lightrail-dev/new/docs/chip_design/NCE_Block_Diagram.md

# NCE (Neural Compute Engine) — Internal Block Diagram

**Document:** LR-NCE-BLK-001  
**Revision:** 1.0  
**Date:** 2026-05-26  
**Process Node:** SMIC 28nm HPC+ / 40nm LL  
**Company:** LightRail AI  

---

## 1. Top-Level Block Diagram

```
+===========================================================================================+
|                              NCE SoC Die (BGA-2500)                                       |
|                                                                                           |
|  +-------+  +-------+  +-------+  +-------+                                              |
|  | JTAG  |  | PMBus |  | SPI   |  | I2C   |     <-- Management I/O (NW corner)           |
|  | Debug |  | Mgmt  |  | Flash |  | Bus   |                                              |
|  +---+---+  +---+---+  +---+---+  +---+---+                                              |
|      |          |          |          |                                                    |
|      +----------+----------+----------+                                                   |
|                 |                                                                         |
|           +-----+------+                                                                  |
|           | System Bus |    AXI4 Interconnect Fabric (250 MHz)                            |
|           | Crossbar   +----------------------------------------------------------+       |
|           +--+---------+--+-----------+--+-----------+--+-----------+--+          |       |
|              |            |             |              |              |            |       |
|              v            v             v              v              v            v       |
|  +-----------+--+ +------+------+ +----+------+ +-----+-----+ +-----+-----+ +----+----+  |
|  | COMPUTE      | | MEMORY      | | PHOTONIC  | | QPA       | | HOST      | | POWER   |  |
|  | CLUSTER      | | SUBSYSTEM   | | I/O       | | CONTROL   | | INTERFACE | | MGMT    |  |
|  +-----------+--+ +------+------+ +----+------+ +-----+-----+ +-----+-----+ +----+----+  |
|              |            |             |              |              |            |       |
|  (detail     |  (detail   |  (detail    |   (detail    |   (detail    |  (detail   |      |
|   below)     |   below)   |   below)    |    below)    |    below)    |   below)   |      |
|              |            |             |              |              |            |       |
+===========================================================================================+
```

---

## 2. Compute Cluster Block Diagram

```
+=========================================================================+
|                        COMPUTE CLUSTER                                  |
|                                                                         |
|  +------------------------------------------------------------------+  |
|  |                    Instruction Frontend                           |  |
|  |  +----------------+  +-----------------+  +-------------------+  |  |
|  |  | Instr Fetch    |  | Instr Decode    |  | Issue / Dispatch  |  |  |
|  |  | Unit (IFU)     |->| Unit (IDU)      |->| Unit              |  |  |
|  |  | L1 I$ 64KB     |  | bfloat16/24     |  | In-order SIMD     |  |  |
|  |  | 4-way assoc    |  | INT8, FP32      |  | Scalar bypass     |  |  |
|  |  +----------------+  +-----------------+  +--------+----------+  |  |
|  +------------------------------------------------------------------+  |
|                                                       |                |
|                                    +------------------+--------+       |
|                                    |                           |       |
|                                    v                           v       |
|  +----------------------------------+   +------------------------+     |
|  |     SIMD Execution Engine        |   | Scalar Execution Unit  |     |
|  |                                  |   |                        |     |
|  |  +----------------------------+  |   | +--------------------+ |     |
|  |  | 128-way SIMD Array         |  |   | | ALU (INT/FP)       | |     |
|  |  | 8 clusters x 16 lanes     |  |   | | Branch Unit        | |     |
|  |  |                            |  |   | | Address Gen        | |     |
|  |  | Each lane:                 |  |   | +--------------------+ |     |
|  |  |   bfloat16 MAC unit        |  |   +------------------------+     |
|  |  |   bfloat24 MAC unit        |  |                                  |
|  |  |   INT8 MAC unit (4x pack)  |  |                                  |
|  |  |   FP32 accumulator         |  |                                  |
|  |  +----------------------------+  |                                  |
|  |                                  |                                  |
|  |  +----------------------------+  |                                  |
|  |  | Register File              |  |                                  |
|  |  | 16x Matrix Regs (256-bit)  |  |                                  |
|  |  | 16x Vector Regs (256-bit)  |  |                                  |
|  |  | 8x Scalar Regs (64-bit)    |  |                                  |
|  |  +----------------------------+  |                                  |
|  +----------------------------------+                                  |
|                     |                                                  |
|                     v                                                  |
|  +----------------------------------+                                  |
|  |      Memory Access Pipeline      |                                  |
|  |  +-------------+  +----------+   |                                  |
|  |  | Load/Store  |  | L1 D$    |   |                                  |
|  |  | Unit (LSU)  |->| 128 KB   |   |                                  |
|  |  | Scatter/    |  | 8-way    |   |                                  |
|  |  | Gather      |  | assoc    |   |                                  |
|  |  +-------------+  +----+-----+   |                                  |
|  +----------------------------------+                                  |
|                            |                                           |
|                            v                                           |
|  +----------------------------------+                                  |
|  |       L2 Cache (Shared)          |                                  |
|  |  16 MB, 8-way, inclusive         |                                  |
|  |  64-byte lines, write-back       |                                  |
|  |  4 DMA channels (scatter-gather) |                                  |
|  +----------------------------------+                                  |
|                                                                        |
+========================================================================+
```

**Function:** Executes AI/ML tensor operations (matrix multiply, convolution,
activation) on streaming data. The 128-way SIMD array processes 128 bfloat16
multiply-accumulate operations per cycle. Data flows from HBM5 through the
cache hierarchy into the register file, and results can be sent to the TFLN
photonic I/O for distributed all-reduce.

---

## 3. Memory Subsystem Block Diagram (HBM5)

```
+=========================================================================+
|                      MEMORY SUBSYSTEM (HBM5)                            |
|                                                                         |
|  +------------------------------------------------------------------+  |
|  |                 L3 / Last-Level Cache                             |  |
|  |  64 MB, 16-way set-associative, exclusive of L2                  |  |
|  |  128-byte lines, write-back, pseudo-LRU                          |  |
|  |  Coherence: MOESI (for CXL.mem shared memory)                    |  |
|  +---+------------------------------------------+-------------------+  |
|      |                                          |                      |
|      v                                          v                      |
|  +---+------------------------+  +--------------+-------------------+  |
|  | HBM5 Memory Scheduler      |  | HBM5 Side-Channel Controller    |  |
|  | & Request Queue             |  |                                  |  |
|  | - 4-entry queue per PC      |  | - REFCK_P/N generation           |  |
|  | - Age-based priority        |  | - CATTRIP / PWR_GOOD monitoring  |  |
|  | - Bank interleaving (32 bk) |  | - IEEE 1500 JTAG                 |  |
|  | - Per-bank refresh w/ temp  |  | - Temperature readout            |  |
|  |   compensation (1x/2x/4x)  |  | - Stack power management         |  |
|  | - R/W turnaround (tWTR/tRTW)|  |                                  |  |
|  +---+------------------------+  +---+------------------------------+  |
|      |                               |                                 |
|      v                               |                                 |
|  +---+-----------------------------+ |                                 |
|  | HBM5 Inline ECC Engine          | |                                 |
|  | - SECDED per 64-bit granule     | |                                 |
|  | - CE/UE counters & interrupt    | |                                 |
|  | - Background scrub (optional)   | |                                 |
|  +---+-----------------------------+ |                                 |
|      |                               |                                 |
|      v                               v                                 |
|  +---+-------------------------------------------------+               |
|  |           HBM5 PHY Controller                       |               |
|  |                                                     |               |
|  |  Stack 0         Stack 1         Stack 2         Stack 3            |
|  |  +------------+  +------------+  +------------+  +------------+    |
|  |  |16-Hi, 16PC |  |16-Hi, 16PC |  |16-Hi, 16PC |  |16-Hi, 16PC |    |
|  |  |1024b/PC    |  |1024b/PC    |  |1024b/PC    |  |1024b/PC    |    |
|  |  |8 Gbps/pin  |  |8 Gbps/pin  |  |8 Gbps/pin  |  |8 Gbps/pin  |    |
|  |  |1.28 TB/s   |  |1.28 TB/s   |  |1.28 TB/s   |  |1.28 TB/s   |    |
|  |  |64 GB       |  |64 GB       |  |64 GB       |  |64 GB       |    |
|  |  +------------+  +------------+  +------------+  +------------+    |
|  |                                                     |               |
|  |  Total: 64 PCs, 5.12 TB/s aggregate, 256 GB         |               |
|  |  (All lanes routed on silicon interposer)            |               |
|  +-----------------------------------------------------+               |
|                                                                         |
|  Data Storage Path:                                                     |
|    CXL -> AXI -> Scheduler -> ACT -> tRCD -> WR -> DQ+ECC -> DRAM      |
|                                                                         |
|  Data Retrieval Path:                                                   |
|    DRAM -> DQ -> ECC Check -> Scheduler -> L1/L2/RegFile/CXL Read       |
|                                                                         |
+=========================================================================+
```

**Function:** Provides 5.12 TB/s memory bandwidth to the compute cluster via
four HBM5 16-Hi stacks (64 pseudo-channels total, 256 GB capacity). The L3
cache serves as a victim cache for L2 misses. The memory scheduler implements
per-PC request queuing with age-based priority, bank-level parallelism,
read/write turnaround optimization, inline SECDED ECC, and temperature-
compensated per-bank refresh for data integrity and retention.

---

## 4. Photonic I/O Subsystem Block Diagram

```
+=========================================================================+
|                    PHOTONIC I/O SUBSYSTEM                               |
|                                                                         |
|  +------------------------------------------------------------------+  |
|  |                     TX Path (8 channels)                          |  |
|  |                                                                   |  |
|  |  +----------+  +----------+  +----------+  +----------+          |  |
|  |  | TX DSP   |  | PAM4     |  | DAC      |  | RF Drive |  --> To  |  |
|  |  | 3-tap    |->| Encoder  |->| (SerDes  |->| Buffer   |  TFLN   |  |
|  |  | FFE      |  |          |  |  analog) |  | +/- 1.5V |  PIC    |  |
|  |  +----------+  +----------+  +----------+  +----------+          |  |
|  |                                                                   |  |
|  +------------------------------------------------------------------+  |
|                                                                         |
|  +------------------------------------------------------------------+  |
|  |                     RX Path (8 channels)                          |  |
|  |                                                                   |  |
|  |  From   +----------+  +----------+  +----------+  +----------+   |  |
|  |  TFLN ->| TIA /    |->| ADC      |->| PAM4     |->| RX DSP   |   |  |
|  |  PIC    | AGC      |  | (SerDes  |  | Decoder  |  | CTLE +   |   |  |
|  |         |          |  |  analog) |  |          |  | 7-tap DFE|   |  |
|  |         +----------+  +----------+  +----------+  +----------+   |  |
|  |                                                                   |  |
|  +------------------------------------------------------------------+  |
|                                                                         |
|  +------------------------------------------------------------------+  |
|  |                   CDR & Link Training                             |  |
|  |                                                                   |  |
|  |  +-------------------+  +-------------------+                     |  |
|  |  | Clock Data        |  | Link Training     |                     |  |
|  |  | Recovery (CDR)    |  | State Machine     |                     |  |
|  |  | per-lane          |  | Auto-negotiation  |                     |  |
|  |  | 0.1 UI tolerance  |  | Loopback modes    |                     |  |
|  |  +-------------------+  +-------------------+                     |  |
|  |                                                                   |  |
|  +------------------------------------------------------------------+  |
|                                                                         |
|  Channel Summary:                                                       |
|  8 TX + 8 RX = 16 lanes total                                          |
|  200 Gbps PAM4 per lane = 1.6 Tbps half-duplex                         |
|  Direct-drive to TFLN modulator (zero-copper datapath)                  |
|  1550 nm C-band DWDM, 100 GHz channel spacing                          |
|                                                                         |
+=========================================================================+
```

**Function:** Converts electrical data from the compute cluster into optical
signals via direct-drive TFLN modulators. The TX path applies DSP equalization,
encodes to PAM4, and drives the TFLN MZI electrodes. The RX path receives
optical signals from photodetectors, digitizes, and recovers data with adaptive
equalization.

---

## 5. QPA Control Subsystem Block Diagram

```
+=========================================================================+
|                    QPA CONTROL SUBSYSTEM                                |
|                                                                         |
|  CXL 2.0 Memory-Mapped Interface                                       |
|  Base: 0x0000_1000                                                      |
|                                                                         |
|  +------------------------------------------------------------------+  |
|  |              CXL Register Decoder                                 |  |
|  |                                                                   |  |
|  |  0x1000: PHASE_SET      -- Write phase vector into shadow buffer  |  |
|  |  0x1004: TRIGGER_EXEC   -- Atomic commit shadow -> DAC bus        |  |
|  |  0x1008: STATUS         -- Read trigger state & channel health    |  |
|  |  0x100C: FAULT_MASK     -- Per-channel fault enable mask          |  |
|  |  0x1010: TELEMETRY_CTRL -- Telemetry sampling on/off              |  |
|  +---+------+----------+--------+------+----------------------------+  |
|      |      |          |        |      |                               |
|      v      v          |        v      v                               |
|  +---+---+ +--+--+     |  +----+---+ ++----+                          |
|  |Shadow | |Trig | |   |  |Fault   | |Telem|                          |
|  |Buffer | |Pipe | |   |  |Mask    | |Ctrl |                          |
|  |128-bit| |line | |   |  |Reg     | |Reg  |                          |
|  +---+---+ +--+--+     |  +----+---+ +--+--+                          |
|      |        |         |       |        |                             |
|      v        v         |       v        v                             |
|  +---+--------+---+    |  +----+--------+---+                         |
|  | DAC Phase Bus  |    |  | Telemetry Status |                        |
|  | 8ch x 16-bit   |    |  | {fault_cnt[15:0],|                        |
|  | Zero-skew sync |    |  |  trig_cnt[15:0]} |                        |
|  +-------+---------+    |  +-----------------+                         |
|          |              |                                              |
|          v              v                                              |
|  +-------+---------+  +---+-------------------+                       |
|  | 100 GHz DACs    |  | SNSPD Fault Detector  |                       |
|  | (external)      |  | 3 dB drop detection   |                       |
|  | Interleaved     |  | Per-channel latch      |                       |
|  +-----------------+  | Auto-reroute output    |                       |
|                       +------------------------+                       |
|                                                                        |
+=========================================================================+
```

**Function:** Provides real-time programmable control of the MZI photonic mesh.
The shadow buffer allows atomic updates of all phase channels simultaneously.
A one-cycle pipeline ensures zero-skew synchronization between phase setting
and DAC trigger. SNSPD feedback detects optical power drops and triggers
automatic waveguide rerouting.

---

## 6. Host Interface Block Diagram

```
+=========================================================================+
|                      HOST INTERFACE                                     |
|                                                                         |
|  +------------------------------------------------------------------+  |
|  |              PCIe Gen 6.0 Root Complex                            |  |
|  |                                                                   |  |
|  |  Port 0 (x16)                    Port 1 (x16)                    |  |
|  |  +-------------------+           +-------------------+           |  |
|  |  | 16 lanes          |           | 16 lanes          |           |  |
|  |  | 64 GT/s PAM4      |           | 64 GT/s PAM4      |           |  |
|  |  | 128 GB/s bidir    |           | 128 GB/s bidir    |           |  |
|  |  +-------------------+           +-------------------+           |  |
|  |                                                                   |  |
|  +------------------------------------------------------------------+  |
|                                                                         |
|  +------------------------------------------------------------------+  |
|  |              CXL 2.0 Controller (Type 2)                          |  |
|  |                                                                   |  |
|  |  +-------------+  +-------------+  +-------------+               |  |
|  |  | CXL.io      |  | CXL.cache   |  | CXL.mem     |               |  |
|  |  | (PCIe TLP)  |  | (coherent   |  | (shared     |               |  |
|  |  |             |  |  cache)     |  |  memory)    |               |  |
|  |  +-------------+  +-------------+  +-------------+               |  |
|  |                                                                   |  |
|  +------------------------------------------------------------------+  |
|                                                                         |
|  +------------------------------------------------------------------+  |
|  |              Debug & Management                                   |  |
|  |                                                                   |  |
|  |  +----------+  +----------+  +----------+  +----------+          |  |
|  |  | JTAG     |  | PMBus    |  | I2C      |  | SPI      |          |  |
|  |  | IEEE1149 |  | 1.3.1    |  | 400 kHz  |  | Flash    |          |  |
|  |  | IEEE1500 |  | VRM tele |  | HBM4 SPD |  | FW boot  |          |  |
|  |  +----------+  +----------+  +----------+  +----------+          |  |
|  |                                                                   |  |
|  +------------------------------------------------------------------+  |
|                                                                         |
+=========================================================================+
```

---
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
