lightrail-dev/new/fab/Dual_NCE_Accelerator_Fab_Release_v1/assembly/Dual_NCE_Accelerator_BOM.csv

Item | Designator | Quantity | Value | Footprint | Manufacturer | MPN | Distributor | DistributorPN | Package | Description | DNP
1 | ? | 1 | MountingHole:MountingHole_3.2mm_M3 | M3 Mounting Hole |  |  |  |  | M3 Mounting Hole |  | No
2 | ? | 1 | MountingHole:MountingHole_3.2mm_M3 | M3 Mounting Hole |  |  |  |  | M3 Mounting Hole |  | No
3 | ? | 1 | MountingHole:MountingHole_3.2mm_M3 | M3 Mounting Hole |  |  |  |  | M3 Mounting Hole |  | No
4 | ? | 1 | MountingHole:MountingHole_3.2mm_M3 | M3 Mounting Hole |  |  |  |  | M3 Mounting Hole |  | No
5 | ? | 1 | MountingHole:MountingHole_3.2mm_M3 | M3 Mounting Hole |  |  |  |  | M3 Mounting Hole |  | No
6 | ? | 1 | MountingHole:MountingHole_3.2mm_M3 | M3 Mounting Hole |  |  |  |  | M3 Mounting Hole |  | No
7 | ? | 1 | MountingHole:MountingHole_3.2mm_M3 | M3 Mounting Hole |  |  |  |  | M3 Mounting Hole |  | No
8 | ? | 1 | MountingHole:MountingHole_3.2mm_M3 | M3 Mounting Hole |  |  |  |  | M3 Mounting Hole |  | No
9 | ? | 1 | MountingHole:MountingHole_3.2mm_M3 | M3 Mounting Hole |  |  |  |  | M3 Mounting Hole |  | No
10 | ? | 1 | MountingHole:MountingHole_3.2mm_M3 | M3 Mounting Hole |  |  |  |  | M3 Mounting Hole |  | No
11 | ? | 1 | MountingHole:MountingHole_3.2mm_M3 | M3 Mounting Hole |  |  |  |  | M3 Mounting Hole |  | No
12 | ? | 1 | MountingHole:MountingHole_3.2mm_M3 | M3 Mounting Hole |  |  |  |  | M3 Mounting Hole |  | No
13 | ? | 1 | LightRail:NCE_BGA2500_40x40mm | BGA-2500 |  |  |  |  | BGA-2500 |  | No
14 | ? | 1 | LightRail:NCE_BGA2500_40x40mm | BGA-2500 |  |  |  |  | BGA-2500 |  | No
15 | ? | 1 | LightRail:TFLN_PIC_17x17mm | TFLN_PIC_17x17mm |  |  |  |  | TFLN_PIC_17x17mm |  | No
16 | ? | 1 | LightRail:TFLN_PIC_17x17mm | TFLN_PIC_17x17mm |  |  |  |  | TFLN_PIC_17x17mm |  | No
17 | ? | 1 | LightRail:DrMOS_PowerPAK_8x8mm | DrMOS_PowerPAK_8x8mm | Renesas | ISL99390FRZ |  |  | DrMOS_PowerPAK_8x8mm | DrMOS Power Stage 60A | No
18 | ? | 1 | LightRail:DrMOS_PowerPAK_8x8mm | DrMOS_PowerPAK_8x8mm | Renesas | ISL99390FRZ |  |  | DrMOS_PowerPAK_8x8mm | DrMOS Power Stage 60A | No
19 | ? | 1 | LightRail:DrMOS_PowerPAK_8x8mm | DrMOS_PowerPAK_8x8mm | Renesas | ISL99390FRZ |  |  | DrMOS_PowerPAK_8x8mm | DrMOS Power Stage 60A | No
20 | ? | 1 | LightRail:DrMOS_PowerPAK_8x8mm | DrMOS_PowerPAK_8x8mm | Renesas | ISL99390FRZ |  |  | DrMOS_PowerPAK_8x8mm | DrMOS Power Stage 60A | No
21 | ? | 1 | LightRail:DrMOS_PowerPAK_8x8mm | DrMOS_PowerPAK_8x8mm | Renesas | ISL99390FRZ |  |  | DrMOS_PowerPAK_8x8mm | DrMOS Power Stage 60A | No
22 | ? | 1 | LightRail:DrMOS_PowerPAK_8x8mm | DrMOS_PowerPAK_8x8mm | Renesas | ISL99390FRZ |  |  | DrMOS_PowerPAK_8x8mm | DrMOS Power Stage 60A | No
23 | ? | 1 | LightRail:DrMOS_PowerPAK_8x8mm | DrMOS_PowerPAK_8x8mm | Renesas | ISL99390FRZ |  |  | DrMOS_PowerPAK_8x8mm | DrMOS Power Stage 60A | No
24 | ? | 1 | LightRail:DrMOS_PowerPAK_8x8mm | DrMOS_PowerPAK_8x8mm | Renesas | ISL99390FRZ |  |  | DrMOS_PowerPAK_8x8mm | DrMOS Power Stage 60A | No
25 | ? | 1 | LightRail:DrMOS_PowerPAK_8x8mm | DrMOS_PowerPAK_8x8mm | Renesas | ISL99390FRZ |  |  | DrMOS_PowerPAK_8x8mm | DrMOS Power Stage 60A | No
26 | ? | 1 | LightRail:DrMOS_PowerPAK_8x8mm | DrMOS_PowerPAK_8x8mm | Renesas | ISL99390FRZ |  |  | DrMOS_PowerPAK_8x8mm | DrMOS Power Stage 60A | No
27 | ? | 1 | LightRail:DrMOS_PowerPAK_8x8mm | DrMOS_PowerPAK_8x8mm | Renesas | ISL99390FRZ |  |  | DrMOS_PowerPAK_8x8mm | DrMOS Power Stage 60A | No
28 | ? | 1 | LightRail:DrMOS_PowerPAK_8x8mm | DrMOS_PowerPAK_8x8mm | Renesas | ISL99390FRZ |  |  | DrMOS_PowerPAK_8x8mm | DrMOS Power Stage 60A | No
29 | ? | 1 | LightRail:DrMOS_PowerPAK_8x8mm | DrMOS_PowerPAK_8x8mm | Renesas | ISL99390FRZ |  |  | DrMOS_PowerPAK_8x8mm | DrMOS Power Stage 60A | No
30 | ? | 1 | LightRail:DrMOS_PowerPAK_8x8mm | DrMOS_PowerPAK_8x8mm | Renesas | ISL99390FRZ |  |  | DrMOS_PowerPAK_8x8mm | DrMOS Power Stage 60A | No
31 | ? | 1 | LightRail:DrMOS_PowerPAK_8x8mm | DrMOS_PowerPAK_8x8mm | Renesas | ISL99390FRZ |  |  | DrMOS_PowerPAK_8x8mm | DrMOS Power Stage 60A | No
32 | ? | 1 | LightRail:DrMOS_PowerPAK_8x8mm | DrMOS_PowerPAK_8x8mm | Renesas | ISL99390FRZ |  |  | DrMOS_PowerPAK_8x8mm | DrMOS Power Stage 60A | No
33 | ? | 1 | LightRail:DrMOS_PowerPAK_8x8mm | DrMOS_PowerPAK_8x8mm | Renesas | ISL99390FRZ |  |  | DrMOS_PowerPAK_8x8mm | DrMOS Power Stage 60A | No
34 | ? | 1 | LightRail:DrMOS_PowerPAK_8x8mm | DrMOS_PowerPAK_8x8mm | Renesas | ISL99390FRZ |  |  | DrMOS_PowerPAK_8x8mm | DrMOS Power Stage 60A | No
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
1658 | ? | 1 | C_passive | C_passive |  |  |  |  | C_passive |  | No
1659 | ? | 1 | C_passive | C_passive |  |  |  |  | C_passive |  | No
1660 | ? | 1 | C_passive | C_passive |  |  |  |  | C_passive |  | No
1661 | ? | 1 | C_passive | C_passive |  |  |  |  | C_passive |  | No
1662 | ? | 1 | C_passive | C_passive |  |  |  |  | C_passive |  | No
1663 | ? | 1 | C_passive | C_passive |  |  |  |  | C_passive |  | No
1664 | ? | 1 | C_passive | C_passive |  |  |  |  | C_passive |  | No
1665 | ? | 1 | C_passive | C_passive |  |  |  |  | C_passive |  | No
1666 | ? | 1 | C_passive | C_passive |  |  |  |  | C_passive |  | No
1667 | ? | 1 | C_passive | C_passive |  |  |  |  | C_passive |  | No
1668 | ? | 1 | C_passive | C_passive |  |  |  |  | C_passive |  | No
1669 | ? | 1 | C_passive | C_passive |  |  |  |  | C_passive |  | No
1670 | ? | 1 | C_passive | C_passive |  |  |  |  | C_passive |  | No
1671 | ? | 1 | C_passive | C_passive |  |  |  |  | C_passive |  | No
1672 | ? | 1 | C_passive | C_passive |  |  |  |  | C_passive |  | No
1673 | ? | 1 | C_passive | C_passive |  |  |  |  | C_passive |  | No
1674 | ? | 1 | C_passive | C_passive |  |  |  |  | C_passive |  | No
1675 | ? | 1 | C_passive | C_passive |  |  |  |  | C_passive |  | No
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
