lightrail-dev/new/tinytapeout/reports/metrics.csv

design | design_name | config | flow_status | total_runtime | routed_runtime | (Cell/mm^2)/Core_Util | DIEAREA_mm^2 | CellPer_mm^2 | OpenDP_Util | Final_Util | Peak_Memory_Usage_MB | synth_cell_count | tritonRoute_violations | Short_violations | MetSpc_violations | OffGrid_violations | MinHole_violations | Other_violations | Magic_violations | pin_antenna_violations | net_antenna_violations | lvs_total_errors | cvc_total_errors | klayout_violations | wire_length | vias | wns | pl_wns | optimized_wns | fastroute_wns | spef_wns | tns | pl_tns | optimized_tns | fastroute_tns | spef_tns | HPWL | routing_layer1_pct | routing_layer2_pct | routing_layer3_pct | routing_layer4_pct | routing_layer5_pct | routing_layer6_pct | wires_count | wire_bits | public_wires_count | public_wire_bits | memories_count | memory_bits | processes_count | cells_pre_abc | AND | DFF | NAND | NOR | OR | XOR | XNOR | MUX
/openlane/designs/tt_um_lightrail_nce | tt_um_lightrail_nce | run1 | flow completed | 0h2m16s0ms | 0h1m51s0ms | 95796.53706657636 | 0.01795472 | 38318.614826630546 | 38.11 | 35.9581 | 532.3 | 662 | 0 | 0 | 0 | 0 | 0 | 0 | 0 | 0 | 0 | 0 | -1 | -1 | 15459 | 4699 | 0.0 | -1 | -1 | -1 | -1 | 0.0 | -1 | -1 | -1 | -1 | 11815352.0 | 0.0 | 34.74 | 23.68 | 4.56 | 0.0 | 0.0 | 594 | 686 | 19 | 111 | 0 | 0 | 0 | 624 | 45 | 0 | 39 | 7 | 73 | 122 | 25 | 45
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
