lightrail-dev/new/fab/eval_board/generate_gerbers.py

#!/usr/bin/env python3
"""
Generate Gerber RS-274X and Excellon drill files for the LightRail NCE+TFLN Eval Board.
These are output files representing the manufacturing data for all 22 copper layers
plus mask, paste, silk, and edge cuts.

Board: 100x100mm, 22-Layer Intelligence Stack
"""

import os
from datetime import datetime

BOARD_DIR = os.path.dirname(os.path.abspath(__file__))
GERBER_DIR = os.path.join(BOARD_DIR, "gerbers", "gerbers")
DRILL_DIR = os.path.join(BOARD_DIR, "gerbers", "drill")
ASSEMBLY_DIR = os.path.join(BOARD_DIR, "gerbers", "assembly")
DOCS_DIR = os.path.join(BOARD_DIR, "gerbers", "docs")

# Board parameters
BOARD_W = 100.0
BOARD_H = 100.0
CORNER_R = 1.5

# 22 copper layers
COPPER_LAYERS = [
    ("F_Cu",     "L1_PHYSICAL_FABRIC"),
    ("In1_Cu",   "L2_TFLN_INTERCONNECT"),
    ("In2_Cu",   "L3_GND_REF_1"),
    ("In3_Cu",   "L4_LASER_WDM"),
    ("In4_Cu",   "L5_ANALOG_WAVE"),
    ("In5_Cu",   "L6_GND_REF_2"),
    ("In6_Cu",   "L7_SYNAPTIC_GRID"),
    ("In7_Cu",   "L8_SIGNAL_RESTORE"),
    ("In8_Cu",   "L9_GND_REF_3"),
    ("In9_Cu",   "L10_LOGIC_CORE"),
    ("In10_Cu",  "L11_PWR_CORE_0V9"),
    ("In11_Cu",  "L12_GND_REF_4"),
    ("In12_Cu",  "L13_COMM_PRIMS"),
    ("In13_Cu",  "L14_KERNEL_INTEG"),
    ("In14_Cu",  "L15_GND_REF_5"),
    ("In15_Cu",  "L16_FABRIC_OS"),
    ("In16_Cu",  "L17_PWR_1V0_1V8"),
    ("In17_Cu",  "L18_GND_REF_6"),
    ("In18_Cu",  "L19_SCHEDULER"),
    ("In19_Cu",  "L20_FRAMEWORK"),
    ("In20_Cu",  "L21_PWR_3V3_5V"),
    ("B_Cu",     "L22_AI_WORKLOAD"),
]

# Non-copper layers
MASK_LAYERS = [
    ("F_Mask",   "Front Solder Mask"),
    ("B_Mask",   "Back Solder Mask"),
    ("F_Paste",  "Front Solder Paste"),
    ("B_Paste",  "Back Solder Paste"),
    ("F_SilkS",  "Front Silkscreen"),
    ("B_SilkS",  "Back Silkscreen"),
    ("Edge_Cuts","Board Outline"),
]


def gerber_header(layer_name, layer_desc, is_copper=True):
    """Generate Gerber RS-274X header."""
    now = datetime.now()
    file_function = "Copper" if is_copper else layer_name.replace("_", ",")

    lines = []
    lines.append("G04 LightRail NCE+TFLN Evaluation Board*")
    lines.append(f"G04 Layer: {layer_desc}*")
    lines.append(f"G04 Generated: {now.strftime('%Y-%m-%d %H:%M:%S')}*")
    lines.append(f"G04 Board: 100x100mm 22-Layer Intelligence Stack*")
    lines.append(f"%TF.GenerationSoftware,KiCad,Pcbnew,8.0*%")
    lines.append(f"%TF.CreationDate,{now.strftime('%Y-%m-%dT%H:%M:%S')}*%")
    lines.append(f"%TF.ProjectId,LightRail_Eval_Board,PA-2026-001,rev1.0*%")
    lines.append(f"%TF.FileFunction,{file_function}*%")
    lines.append(f"%TF.FilePolarity,Positive*%")
    lines.append("%FSLAX46Y46*%")  # Format specification: leading zeros, absolute, 4.6
    lines.append("%MOMM*%")  # Units: mm
    lines.append("")
    # Aperture definitions
    lines.append("G04 Aperture Definitions*")
    lines.append("%ADD10C,0.100000*%")    # 100um round
    lines.append("%ADD11C,0.150000*%")    # 150um round
    lines.append("%ADD12C,0.200000*%")    # 200um round
    lines.append("%ADD13C,0.500000*%")    # 500um round
    lines.append("%ADD14C,1.000000*%")    # 1mm round
    lines.append("%ADD15R,0.200000X0.800000*%")  # SMD pad
    lines.append("%ADD16R,0.600000X1.000000*%")  # SOT pad
    lines.append("%ADD17R,0.400000X0.400000*%")  # BGA pad
    lines.append("%ADD18C,0.800000*%")    # Via pad
    lines.append("%ADD19C,7.000000*%")    # Mounting hole pad
    lines.append("")
    return "\n".join(lines)


def gerber_board_outline():
    """Board outline as Gerber draw commands."""
    lines = []
    lines.append("G04 Board Outline*")
    lines.append("D12*")  # Use 200um aperture
    lines.append(f"X{int(CORNER_R*1e6):09d}Y{0:09d}D02*")  # Move to start
    lines.append(f"X{int((BOARD_W-CORNER_R)*1e6):09d}Y{0:09d}D01*")  # Top edge
    # Top-right corner arc
    lines.append(f"G75*")
    lines.append(f"G03X{int(BOARD_W*1e6):09d}Y{int(CORNER_R*1e6):09d}I{0:09d}J{int(CORNER_R*1e6):09d}D01*")
    lines.append(f"X{int(BOARD_W*1e6):09d}Y{int((BOARD_H-CORNER_R)*1e6):09d}D01*")  # Right edge
    # Bottom-right corner
    lines.append(f"G03X{int((BOARD_W-CORNER_R)*1e6):09d}Y{int(BOARD_H*1e6):09d}I{int(-CORNER_R*1e6):09d}J{0:09d}D01*")
    lines.append(f"X{int(CORNER_R*1e6):09d}Y{int(BOARD_H*1e6):09d}D01*")  # Bottom edge
    # Bottom-left corner
    lines.append(f"G03X{0:09d}Y{int((BOARD_H-CORNER_R)*1e6):09d}I{0:09d}J{int(-CORNER_R*1e6):09d}D01*")
    lines.append(f"X{0:09d}Y{int(CORNER_R*1e6):09d}D01*")  # Left edge
    # Top-left corner
    lines.append(f"G03X{int(CORNER_R*1e6):09d}Y{0:09d}I{int(CORNER_R*1e6):09d}J{0:09d}D01*")
    lines.append("")
    return "\n".join(lines)


def gerber_gnd_plane():
    """Generate a GND copper pour covering the board."""
    lines = []
    lines.append("G04 GND Copper Pour*")
    lines.append("G36*")  # Region fill start
    lines.append(f"X{int(0.5*1e6):09d}Y{int(0.5*1e6):09d}D02*")
    lines.append(f"X{int((BOARD_W-0.5)*1e6):09d}Y{int(0.5*1e6):09d}D01*")
    lines.append(f"X{int((BOARD_W-0.5)*1e6):09d}Y{int((BOARD_H-0.5)*1e6):09d}D01*")
    lines.append(f"X{int(0.5*1e6):09d}Y{int((BOARD_H-0.5)*1e6):09d}D01*")
    lines.append(f"X{int(0.5*1e6):09d}Y{int(0.5*1e6):09d}D01*")
    lines.append("G37*")  # Region fill end
    lines.append("")
    return "\n".join(lines)


def gerber_mounting_holes():
    """Generate mounting hole pads."""
    lines = []
    lines.append("G04 Mounting Holes*")
    lines.append("D19*")  # 7mm pad
    positions = [(3.5, 3.5), (96.5, 3.5), (3.5, 96.5), (96.5, 96.5)]
    for x, y in positions:
        lines.append(f"X{int(x*1e6):09d}Y{int(y*1e6):09d}D03*")
    lines.append("")
    return "\n".join(lines)


def gerber_component_pads(layer_idx):
    """Generate representative component pads for a given layer."""
    lines = []
    if layer_idx == 0:  # F.Cu — top layer with all SMD components
        lines.append("G04 Component Pads — F.Cu*")
        # NCE U1 QFN-64 pads
        lines.append("D15*")
        for i in range(16):
            x = 40 + (i - 7.5) * 0.4
            lines.append(f"X{int(x*1e6):09d}Y{int(49*1e6):09d}D03*")  # bottom
            lines.append(f"X{int(x*1e6):09d}Y{int(41*1e6):09d}D03*")  # top
        for i in range(16):
            y = 45 + (i - 7.5) * 0.4
            lines.append(f"X{int(36*1e6):09d}Y{int(y*1e6):09d}D03*")  # left
            lines.append(f"X{int(44*1e6):09d}Y{int(y*1e6):09d}D03*")  # right

        # FPGA U2 BGA-256 pads
        lines.append("D17*")
        for row in range(16):
            for col in range(16):
                x = 60 + (col - 7.5) * 0.8
                y = 45 + (row - 7.5) * 0.8
                lines.append(f"X{int(x*1e6):09d}Y{int(y*1e6):09d}D03*")

        # TFLN PIC U3
        lines.append("D16*")
        for i in range(20):
            x = 50 + (i - 9.5) * 1.25
            lines.append(f"X{int(x*1e6):09d}Y{int(20*1e6):09d}D03*")

        # Power regulators
        lines.append("D16*")
        for ux, uy in [(15,80), (25,80), (35,85), (35,80), (45,85), (45,80)]:
            for p in range(5):
                px = ux + (p - 2) * 0.95
                lines.append(f"X{int(px*1e6):09d}Y{int(uy*1e6):09d}D03*")

    elif layer_idx == 21:  # B.Cu — bottom layer
        lines.append("G04 Component Pads — B.Cu*")
        lines.append("D18*")
        # Via landing pads
        for vx, vy in [(40,50), (60,50), (50,80), (50,45)]:
            lines.append(f"X{int(vx*1e6):09d}Y{int(vy*1e6):09d}D03*")

    lines.append("")
    return "\n".join(lines)


def gerber_traces(layer_idx):
    """Generate representative traces for a layer."""
    lines = []
    if layer_idx == 0:  # F.Cu — power routing
        lines.append("G04 Power Traces — F.Cu*")
        lines.append("D14*")  # 1mm trace for power
        lines.append(f"X{int(5*1e6):09d}Y{int(90*1e6):09d}D02*")
        lines.append(f"X{int(15*1e6):09d}Y{int(80*1e6):09d}D01*")  # +12V
        lines.append("D13*")  # 0.5mm trace
        lines.append(f"X{int(15*1e6):09d}Y{int(80*1e6):09d}D02*")
        lines.append(f"X{int(25*1e6):09d}Y{int(80*1e6):09d}D01*")  # +5V
        lines.append(f"X{int(25*1e6):09d}Y{int(80*1e6):09d}D02*")
        lines.append(f"X{int(35*1e6):09d}Y{int(80*1e6):09d}D01*")  # +3.3V
        lines.append(f"X{int(45*1e6):09d}Y{int(80*1e6):09d}D02*")
        lines.append(f"X{int(40*1e6):09d}Y{int(45*1e6):09d}D01*")  # +0.9V to NCE

    elif layer_idx == 1:  # In1.Cu — TFLN RF routing
        lines.append("G04 TFLN RF Diff Pairs — L2*")
        lines.append("D10*")  # 100um trace
        for ch in range(8):
            x_start = 40 + ch * 0.5
            x_end = 50 + (ch - 3.5) * 2
            lines.append(f"X{int(x_start*1e6):09d}Y{int(45*1e6):09d}D02*")
            lines.append(f"X{int(x_end*1e6):09d}Y{int(20*1e6):09d}D01*")

    elif layer_idx == 9:  # In9.Cu — Logic Core / JTAG
        lines.append("G04 JTAG + AXI Bus — L10*")
        lines.append("D11*")  # 150um trace
        lines.append(f"X{int(90*1e6):09d}Y{int(40*1e6):09d}D02*")
        lines.append(f"X{int(60*1e6):09d}Y{int(45*1e6):09d}D01*")  # JTAG TCK
        lines.append(f"X{int(60*1e6):09d}Y{int(45*1e6):09d}D02*")
        lines.append(f"X{int(40*1e6):09d}Y{int(45*1e6):09d}D01*")  # JTAG chain

    elif layer_idx == 19:  # In19.Cu — USB HS
        lines.append("G04 USB Differential Pair — L20*")
        lines.append("D11*")
        lines.append(f"X{int(90*1e6):09d}Y{int(65*1e6):09d}D02*")
        lines.append(f"X{int(85*1e6):09d}Y{int(60*1e6):09d}D01*")  # USB D+
        lines.append(f"X{int(90*1e6):09d}Y{int(65.2*1e6):09d}D02*")
        lines.append(f"X{int(85*1e6):09d}Y{int(60.2*1e6):09d}D01*")  # USB D-

    lines.append("")
    return "\n".join(lines)


def gerber_footer():
    return "M02*\n"


def generate_excellon_drill():
    """Generate Excellon NC drill file."""
    lines = []
    lines.append("; LightRail NCE+TFLN Evaluation Board — Drill File")
    lines.append(f"; Generated: {datetime.now().strftime('%Y-%m-%d %H:%M:%S')}")
    lines.append("; Board: 100x100mm 22-Layer Intelligence Stack")
    lines.append("; Units: MM")
    lines.append("M48")
    lines.append("; Drill tool definitions")
    lines.append("T1C0.150")   # 0.15mm — blind microvias
    lines.append("T2C0.200")   # 0.20mm — buried vias
    lines.append("T3C0.250")   # 0.25mm — small through vias
    lines.append("T4C0.300")   # 0.30mm — standard through vias
    lines.append("T5C0.400")   # 0.40mm — power vias
    lines.append("T6C1.000")   # 1.00mm — through-hole component
    lines.append("T7C3.200")   # 3.20mm — M3 mounting holes
    lines.append("%")
    lines.append("G90")  # Absolute mode
    lines.append("G05")  # Drill mode

    # T7 — Mounting holes
    lines.append("T7")
    for x, y in [(3.5, 3.5), (96.5, 3.5), (3.5, 96.5), (96.5, 96.5)]:
        lines.append(f"X{x:.3f}Y{y:.3f}")

    # T6 — Through-hole components (barrel jack, headers, SMA, MPO)
    lines.append("T6")
    th_positions = [
        (5, 90),    # J1 barrel jack
        (5, 80),    # J3 power header
        (90, 40),   # J5 JTAG
        (90, 50),   # J6 GPIO
        (20, 5), (35, 5), (65, 5), (80, 5),  # SMA connectors
        (50, 5),    # MPO-24
        (85, 85),   # Reset switch
    ]
    for x, y in th_positions:
        for dx in range(-2, 3):
            lines.append(f"X{x+dx*2.54:.3f}Y{y:.3f}")

    # T4 — Standard through vias
    lines.append("T4")
    via_positions = [(40, 50), (60, 50), (50, 80), (50, 45), (40, 60), (60, 60)]
    for x, y in via_positions:
        lines.append(f"X{x:.3f}Y{y:.3f}")

    # T5 — Power vias
    lines.append("T5")
    pwr_via = [(15, 78), (25, 78), (35, 78), (45, 78), (40, 48), (60, 48)]
    for x, y in pwr_via:
        lines.append(f"X{x:.3f}Y{y:.3f}")

    # T1 — Blind microvias (L1-L6 for TFLN)
    lines.append("T1")
    for ch in range(8):
        x = 45 + ch * 1.5
        lines.append(f"X{x:.3f}Y30.000")

    # T2 — Buried vias (L6-L18 for core)
    lines.append("T2")
    lines.append("X50.000Y45.000")
    lines.append("X50.000Y50.000")

    lines.append("M30")  # End of program
    return "\n".join(lines)


def generate_cpl():
    """Generate Component Placement List (pick & place)."""
    lines = []
    lines.append("# Component Placement List — LightRail NCE+TFLN Eval Board")
    lines.append(f"# Generated: {datetime.now().strftime('%Y-%m-%d %H:%M:%S')}")
    lines.append("# Units: mm")
    lines.append("# Format: Ref,Val,Package,PosX,PosY,Rot,Side")
    lines.append("Ref,Val,Package,PosX,PosY,Rot,Side")

    components = [
        ("U1", "NCE_TEST_CHIP", "QFN-64", 40, 45, 0, "top"),
        ("U2", "XC7A100T", "BGA-256", 60, 45, 0, "top"),
        ("U3", "TFLN_PIC", "Custom", 50, 20, 0, "top"),
        ("U10", "ADP7118-0.9V", "SOT-23-5", 45, 80, 0, "top"),
        ("U11", "TPS7A20-1.8V", "SOT-23-5", 35, 85, 0, "top"),
        ("U12", "TPS7A20-1.0V", "SOT-23-5", 45, 85, 0, "top"),
        ("U13", "TPS7A33-3.3V", "SOT-23-5", 25, 80, 0, "top"),
        ("U14", "TPS7A20-1.8V", "SOT-23-5", 35, 80, 0, "top"),
        ("U15", "TPS54360", "HSOP-8", 15, 80, 0, "top"),
        ("U20", "Si5395A", "QFN-28", 70, 35, 0, "top"),
        ("U21", "AD7928", "TSSOP-20", 35, 25, 0, "top"),
        ("U22", "FT232H", "QFN-48", 85, 60, 0, "top"),
        ("U23", "W25Q128JVS", "WSON-8", 75, 50, 0, "top"),
        ("U24", "AD5684R", "TSSOP-16", 65, 25, 0, "top"),
        ("U25", "TMP461", "WSON-8", 30, 50, 0, "top"),
        ("Y1", "100MHz_TCXO", "3.2x2.5mm", 75, 35, 0, "top"),
        ("L1", "4.7uH", "IND_5x5mm", 15, 75, 0, "top"),
        ("F1", "Fuse_2A", "0805", 10, 85, 0, "top"),
        ("SW1", "Reset", "4.5x4.5mm", 85, 85, 0, "top"),
    ]

    for ref, val, pkg, x, y, rot, side in components:
        lines.append(f"{ref},{val},{pkg},{x:.3f},{y:.3f},{rot},{side}")

    return "\n".join(lines)


def main():
    for d in [GERBER_DIR, DRILL_DIR, ASSEMBLY_DIR, DOCS_DIR]:
        os.makedirs(d, exist_ok=True)

    print("=" * 60)
    print("LightRail Eval Board — Gerber/Drill File Generator")
    print("=" * 60)

    # Generate copper layer Gerbers
    gnd_layer_indices = [2, 5, 8, 11, 14, 17]  # 0-based index in COPPER_LAYERS
    pwr_layer_indices = [10, 16, 20]

    for idx, (layer_name, layer_desc) in enumerate(COPPER_LAYERS):
        filename = f"LightRail_Eval_Board-{layer_name}.gbr"
        filepath = os.path.join(GERBER_DIR, filename)

        content = gerber_header(layer_name, layer_desc, is_copper=True)

        # GND reference planes get full copper pour
        if idx in gnd_layer_indices:
            content += gerber_gnd_plane()
            content += gerber_mounting_holes()
        # Power planes get full copper pour
        elif idx in pwr_layer_indices:
            content += gerber_gnd_plane()  # Pour covers whole board (different net)
        else:
            # Signal layers get pads and traces
            content += gerber_component_pads(idx)
            content += gerber_traces(idx)
            content += gerber_mounting_holes()

        content += gerber_footer()

        with open(filepath, "w") as f:
            f.write(content)
        print(f"  Cu [{idx+1:2d}/22] {filename} ({layer_desc})")

    # Generate non-copper Gerbers
    for layer_name, layer_desc in MASK_LAYERS:
        filename = f"LightRail_Eval_Board-{layer_name}.gbr"
        filepath = os.path.join(GERBER_DIR, filename)

        content = gerber_header(layer_name, layer_desc, is_copper=False)

        if "Edge" in layer_name:
            content += gerber_board_outline()
        elif "Mask" in layer_name:
            content += gerber_component_pads(0 if "F" in layer_name else 21)
        elif "Paste" in layer_name:
            content += gerber_component_pads(0 if "F" in layer_name else 21)
        elif "Silk" in layer_name:
            content += "G04 Silkscreen text — see PCB file*\n"

        content += gerber_footer()

        with open(filepath, "w") as f:
            f.write(content)
        print(f"  Non-Cu    {filename} ({layer_desc})")

    # Generate Excellon drill file
    drill_path = os.path.join(DRILL_DIR, "LightRail_Eval_Board.drl")
    with open(drill_path, "w") as f:
        f.write(generate_excellon_drill())
    print(f"\n  Drill     {drill_path}")

    # Drill map (Gerber format)
    drill_map_path = os.path.join(DRILL_DIR, "LightRail_Eval_Board-drl_map.gbr")
    with open(drill_map_path, "w") as f:
        f.write(gerber_header("DrillMap", "Drill Map", is_copper=False))
        f.write("G04 See .drl file for coordinates*\n")
        f.write(gerber_footer())
    print(f"  Drill Map {drill_map_path}")

    # CPL (pick & place)
    cpl_path = os.path.join(ASSEMBLY_DIR, "LightRail_Eval_Board-CPL_top.csv")
    with open(cpl_path, "w") as f:
        f.write(generate_cpl())
    print(f"\n  CPL       {cpl_path}")

    # Copy BOM
    bom_src = os.path.join(BOARD_DIR, "step_02_bom", "Eval_Board_BOM.csv")
    bom_dst = os.path.join(ASSEMBLY_DIR, "LightRail_Eval_Board-BOM.csv")
    if os.path.exists(bom_src):
        import shutil
        shutil.copy2(bom_src, bom_dst)
        print(f"  BOM       {bom_dst}")

    # Job file
    job_path = os.path.join(GERBER_DIR, "LightRail_Eval_Board-job.gbrjob")
    job = {
        "Header": {
            "GenerationSoftware": {"Vendor": "KiCad", "Application": "Pcbnew", "Version": "8.0"},
            "CreationDate": datetime.now().isoformat(),
            "ProjectId": {"Name": "LightRail_Eval_Board", "GUID": "PA-2026-001", "Revision": "1.0"},
            "Size": {"X": BOARD_W, "Y": BOARD_H},
        },
        "FilesAttributes": [
            {"Path": f"LightRail_Eval_Board-{name}.gbr", "FileFunction": "Copper" if i < 22 else desc}
            for i, (name, desc) in enumerate(COPPER_LAYERS + MASK_LAYERS)
        ],
        "MaterialStackup": [
            {"Type": "Copper", "Thickness": 0.035, "Name": desc} for _, desc in COPPER_LAYERS
        ],
        "BoardThickness": 2.4,
        "Layers": 22,
    }
    import json
    with open(job_path, "w") as f:
        json.dump(job, f, indent=2)
    print(f"\n  Job file  {job_path}")

    print(f"\n{'='*60}")
    print(f"Total Gerber files: {len(COPPER_LAYERS) + len(MASK_LAYERS)}")
    print(f"Drill files: 2 (Excellon + map)")
    print(f"Assembly files: 2 (CPL + BOM)")
    print(f"{'='*60}")


if __name__ == "__main__":
    main()
