lightrail-dev/new/tinytapeout/gl/tt_um_lightrail_nce.nl.v

// This is the unpowered netlist.
module tt_um_lightrail_nce (clk,
    ena,
    rst_n,
    ui_in,
    uio_in,
    uio_oe,
    uio_out,
    uo_out);
 input clk;
 input ena;
 input rst_n;
 input [7:0] ui_in;
 input [7:0] uio_in;
 output [7:0] uio_oe;
 output [7:0] uio_out;
 output [7:0] uo_out;

 wire net20;
 wire net21;
 wire net22;
 wire net23;
 wire net24;
 wire net25;
 wire net26;
 wire net27;
 wire net28;
 wire net29;
 wire net30;
 wire net31;
 wire net32;
 wire net33;
 wire net34;
 wire net35;
 wire _0000_;
 wire _0001_;
 wire _0002_;
 wire _0003_;
 wire _0004_;
 wire _0005_;
 wire _0006_;
 wire _0007_;
 wire _0008_;
 wire _0009_;
 wire _0010_;
 wire _0011_;
 wire _0012_;
 wire _0013_;
 wire _0014_;
 wire _0015_;
 wire _0016_;
 wire _0017_;
 wire _0018_;
 wire _0019_;
 wire _0020_;
 wire _0021_;
 wire _0022_;
 wire _0023_;
 wire _0024_;
 wire _0025_;
 wire _0026_;
 wire _0027_;
 wire _0028_;
 wire _0029_;
 wire _0030_;
 wire _0031_;
 wire _0032_;
 wire _0033_;
 wire _0034_;
 wire _0035_;
 wire _0036_;
 wire _0037_;
 wire _0038_;
 wire _0039_;
 wire _0040_;
 wire _0041_;
 wire _0042_;
 wire _0043_;
 wire _0044_;
 wire _0045_;
 wire _0046_;
 wire _0047_;
 wire _0048_;
 wire _0049_;
 wire _0050_;
 wire _0051_;
 wire _0052_;
 wire _0053_;
 wire _0054_;
 wire _0055_;
 wire _0056_;
 wire _0057_;
 wire _0058_;
 wire _0059_;
 wire _0060_;
 wire _0061_;
 wire _0062_;
 wire _0063_;
 wire _0064_;
 wire _0065_;
 wire _0066_;
 wire _0067_;
 wire _0068_;
 wire _0069_;
 wire _0070_;
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
 sky130_fd_sc_hd__mux2_1 _0610_ (.A0(\result[1] ),
    .A1(_0601_),
    .S(net8),
    .X(_0602_));
 sky130_fd_sc_hd__clkbuf_1 _0611_ (.A(_0602_),
    .X(net13));
 sky130_fd_sc_hd__dlymetal6s2s_1 _0612_ (.A(\accumulator[7] ),
    .X(_0603_));
 sky130_fd_sc_hd__clkbuf_2 _0613_ (.A(\accumulator[2] ),
    .X(_0604_));
 sky130_fd_sc_hd__or4_1 _0614_ (.A(_0603_),
    .B(_0604_),
    .C(\accumulator[1] ),
    .D(\accumulator[0] ),
    .X(_0033_));
 sky130_fd_sc_hd__clkbuf_2 _0615_ (.A(\accumulator[13] ),
    .X(_0034_));
 sky130_fd_sc_hd__clkbuf_2 _0616_ (.A(\accumulator[12] ),
    .X(_0035_));
 sky130_fd_sc_hd__clkbuf_2 _0617_ (.A(\accumulator[14] ),
    .X(_0036_));
 sky130_fd_sc_hd__clkbuf_2 _0618_ (.A(\accumulator[11] ),
    .X(_0037_));
 sky130_fd_sc_hd__or4b_1 _0619_ (.A(_0601_),
    .B(_0036_),
    .C(_0037_),
    .D_N(net8),
    .X(_0038_));
 sky130_fd_sc_hd__clkbuf_2 _0620_ (.A(\accumulator[10] ),
    .X(_0039_));
 sky130_fd_sc_hd__clkbuf_2 _0621_ (.A(\accumulator[9] ),
    .X(_0040_));
 sky130_fd_sc_hd__clkbuf_2 _0622_ (.A(\accumulator[8] ),
    .X(_0041_));
 sky130_fd_sc_hd__buf_1 _0623_ (.A(\accumulator[6] ),
    .X(_0042_));
 sky130_fd_sc_hd__dlymetal6s2s_1 _0624_ (.A(\accumulator[5] ),
    .X(_0043_));
 sky130_fd_sc_hd__buf_1 _0625_ (.A(\accumulator[4] ),
    .X(_0044_));
 sky130_fd_sc_hd__buf_1 _0626_ (.A(\accumulator[3] ),
    .X(_0045_));
 sky130_fd_sc_hd__or4_1 _0627_ (.A(_0042_),
    .B(_0043_),
    .C(_0044_),
    .D(_0045_),
    .X(_0046_));
 sky130_fd_sc_hd__or4_1 _0628_ (.A(_0039_),
    .B(_0040_),
    .C(_0041_),
    .D(_0046_),
    .X(_0047_));
 sky130_fd_sc_hd__or4_1 _0629_ (.A(_0034_),
    .B(_0035_),
    .C(_0038_),
    .D(_0047_),
    .X(_0048_));
 sky130_fd_sc_hd__or2b_1 _0630_ (.A(_0598_),
    .B_N(\result[2] ),
    .X(_0049_));
 sky130_fd_sc_hd__o21ai_1 _0631_ (.A1(_0033_),
    .A2(_0048_),
    .B1(_0049_),
    .Y(net14));
 sky130_fd_sc_hd__mux2_1 _0632_ (.A0(\result[3] ),
    .A1(overflow),
    .S(net8),
    .X(_0050_));
 sky130_fd_sc_hd__clkbuf_1 _0633_ (.A(_0050_),
    .X(net15));
 sky130_fd_sc_hd__and2b_1 _0634_ (.A_N(_0598_),
    .B(\result[4] ),
    .X(_0051_));
 sky130_fd_sc_hd__clkbuf_1 _0635_ (.A(_0051_),
    .X(net16));
 sky130_fd_sc_hd__and2b_1 _0636_ (.A_N(_0598_),
    .B(\result[5] ),
    .X(_0052_));
 sky130_fd_sc_hd__clkbuf_1 _0637_ (.A(_0052_),
    .X(net17));
 sky130_fd_sc_hd__and2b_1 _0638_ (.A_N(_0598_),
    .B(\result[6] ),
    .X(_0053_));
 sky130_fd_sc_hd__clkbuf_1 _0639_ (.A(_0053_),
    .X(net18));
 sky130_fd_sc_hd__and2b_1 _0640_ (.A_N(_0598_),
    .B(\result[7] ),
    .X(_0054_));
 sky130_fd_sc_hd__clkbuf_1 _0641_ (.A(_0054_),
    .X(net19));
 sky130_fd_sc_hd__buf_1 _0642_ (.A(ui_in[0]),
    .X(_0055_));
 sky130_fd_sc_hd__clkbuf_2 _0643_ (.A(_0055_),
    .X(_0056_));
 sky130_fd_sc_hd__nand2_1 _0644_ (.A(net6),
    .B(net1),
    .Y(_0057_));
 sky130_fd_sc_hd__or2_2 _0645_ (.A(net7),
    .B(_0057_),
    .X(_0058_));
 sky130_fd_sc_hd__clkbuf_2 _0646_ (.A(_0058_),
    .X(_0059_));
 sky130_fd_sc_hd__clkbuf_2 _0647_ (.A(\reg_a[0] ),
    .X(_0060_));
 sky130_fd_sc_hd__buf_2 _0648_ (.A(_0060_),
    .X(_0061_));
 sky130_fd_sc_hd__clkbuf_2 _0649_ (.A(_0061_),
    .X(_0062_));
 sky130_fd_sc_hd__nor2_2 _0650_ (.A(net7),
    .B(_0057_),
    .Y(_0063_));
 sky130_fd_sc_hd__buf_1 _0651_ (.A(_0063_),
    .X(_0064_));
 sky130_fd_sc_hd__or2_1 _0652_ (.A(_0062_),
    .B(_0064_),
    .X(_0065_));
 sky130_fd_sc_hd__dlymetal6s2s_1 _0653_ (.A(rst_n),
    .X(_0066_));
 sky130_fd_sc_hd__clkbuf_2 _0654_ (.A(_0066_),
    .X(_0067_));
 sky130_fd_sc_hd__o211a_1 _0655_ (.A1(_0056_),
    .A2(_0059_),
    .B1(_0065_),
    .C1(_0067_),
    .X(_0000_));
 sky130_fd_sc_hd__clkbuf_2 _0656_ (.A(net2),
    .X(_0068_));
 sky130_fd_sc_hd__clkbuf_2 _0657_ (.A(\reg_a[1] ),
    .X(_0069_));
 sky130_fd_sc_hd__clkbuf_2 _0658_ (.A(_0069_),
    .X(_0070_));
 sky130_fd_sc_hd__or2_1 _0659_ (.A(_0070_),
    .B(_0064_),
    .X(_0071_));
 sky130_fd_sc_hd__o211a_1 _0660_ (.A1(_0068_),
    .A2(_0059_),
    .B1(_0071_),
    .C1(_0067_),
    .X(_0001_));
 sky130_fd_sc_hd__clkbuf_2 _0661_ (.A(ui_in[2]),
    .X(_0072_));
 sky130_fd_sc_hd__clkbuf_2 _0662_ (.A(_0072_),
    .X(_0073_));
 sky130_fd_sc_hd__clkbuf_2 _0663_ (.A(\reg_a[2] ),
    .X(_0074_));
 sky130_fd_sc_hd__clkbuf_2 _0664_ (.A(_0074_),
    .X(_0075_));
 sky130_fd_sc_hd__or2_1 _0665_ (.A(_0075_),
    .B(_0064_),
    .X(_0076_));
 sky130_fd_sc_hd__o211a_1 _0666_ (.A1(_0073_),
    .A2(_0059_),
    .B1(_0076_),
    .C1(_0067_),
    .X(_0002_));
 sky130_fd_sc_hd__clkbuf_2 _0667_ (.A(ui_in[3]),
    .X(_0077_));
 sky130_fd_sc_hd__clkbuf_2 _0668_ (.A(_0077_),
    .X(_0078_));
 sky130_fd_sc_hd__clkbuf_2 _0669_ (.A(\reg_a[3] ),
    .X(_0079_));
 sky130_fd_sc_hd__clkbuf_2 _0670_ (.A(_0079_),
    .X(_0080_));
 sky130_fd_sc_hd__or2_1 _0671_ (.A(_0080_),
    .B(_0064_),
    .X(_0081_));
 sky130_fd_sc_hd__o211a_1 _0672_ (.A1(_0078_),
    .A2(_0059_),
    .B1(_0081_),
    .C1(_0067_),
    .X(_0003_));
 sky130_fd_sc_hd__buf_2 _0673_ (.A(net3),
    .X(_0082_));
 sky130_fd_sc_hd__clkbuf_2 _0674_ (.A(\reg_a[4] ),
    .X(_0083_));
 sky130_fd_sc_hd__clkbuf_2 _0675_ (.A(_0083_),
    .X(_0084_));
 sky130_fd_sc_hd__or2_1 _0676_ (.A(_0084_),
    .B(_0064_),
    .X(_0085_));
 sky130_fd_sc_hd__o211a_1 _0677_ (.A1(_0082_),
    .A2(_0059_),
    .B1(_0085_),
    .C1(_0067_),
    .X(_0004_));
 sky130_fd_sc_hd__dlymetal6s2s_1 _0678_ (.A(ui_in[5]),
    .X(_0086_));
 sky130_fd_sc_hd__buf_2 _0679_ (.A(_0086_),
    .X(_0087_));
 sky130_fd_sc_hd__clkbuf_2 _0680_ (.A(\reg_a[5] ),
    .X(_0088_));
 sky130_fd_sc_hd__buf_2 _0681_ (.A(_0088_),
    .X(_0089_));
 sky130_fd_sc_hd__or2_1 _0682_ (.A(_0089_),
    .B(_0064_),
    .X(_0090_));
 sky130_fd_sc_hd__clkbuf_2 _0683_ (.A(_0066_),
    .X(_0091_));
 sky130_fd_sc_hd__o211a_1 _0684_ (.A1(_0087_),
    .A2(_0059_),
    .B1(_0090_),
    .C1(_0091_),
    .X(_0005_));
 sky130_fd_sc_hd__dlymetal6s2s_1 _0685_ (.A(net4),
    .X(_0092_));
 sky130_fd_sc_hd__clkbuf_2 _0686_ (.A(_0092_),
    .X(_0093_));
 sky130_fd_sc_hd__clkbuf_2 _0687_ (.A(\reg_a[6] ),
    .X(_0094_));
 sky130_fd_sc_hd__or2_1 _0688_ (.A(_0094_),
    .B(_0063_),
    .X(_0095_));
 sky130_fd_sc_hd__o211a_1 _0689_ (.A1(_0093_),
    .A2(_0058_),
    .B1(_0095_),
    .C1(_0091_),
    .X(_0006_));
 sky130_fd_sc_hd__clkbuf_2 _0690_ (.A(net5),
    .X(_0096_));
 sky130_fd_sc_hd__clkbuf_2 _0691_ (.A(_0096_),
    .X(_0097_));
 sky130_fd_sc_hd__clkbuf_2 _0692_ (.A(\reg_a[7] ),
    .X(_0098_));
 sky130_fd_sc_hd__clkbuf_2 _0693_ (.A(_0098_),
    .X(_0099_));
 sky130_fd_sc_hd__clkbuf_2 _0694_ (.A(_0099_),
    .X(_0100_));
 sky130_fd_sc_hd__or2_1 _0695_ (.A(_0100_),
    .B(_0063_),
    .X(_0101_));
 sky130_fd_sc_hd__o211a_1 _0696_ (.A1(_0097_),
    .A2(_0058_),
    .B1(_0101_),
    .C1(_0091_),
    .X(_0007_));
 sky130_fd_sc_hd__and3b_2 _0697_ (.A_N(net6),
    .B(net1),
    .C(net7),
    .X(_0102_));
 sky130_fd_sc_hd__clkbuf_2 _0698_ (.A(_0102_),
    .X(_0103_));
 sky130_fd_sc_hd__o211a_1 _0699_ (.A1(_0063_),
    .A2(_0103_),
    .B1(_0062_),
    .C1(_0056_),
    .X(_0104_));
 sky130_fd_sc_hd__and3_1 _0700_ (.A(\accumulator[0] ),
    .B(_0062_),
    .C(_0056_),
    .X(_0105_));
 sky130_fd_sc_hd__nor3b_1 _0701_ (.A(net6),
    .B(_0105_),
    .C_N(net7),
    .Y(_0106_));
 sky130_fd_sc_hd__nor2_2 _0702_ (.A(_0063_),
    .B(_0102_),
    .Y(_0107_));
 sky130_fd_sc_hd__clkbuf_2 _0703_ (.A(_0107_),
    .X(_0108_));
 sky130_fd_sc_hd__o221a_1 _0704_ (.A1(net36),
    .A2(_0104_),
    .B1(_0106_),
    .B2(_0108_),
    .C1(_0091_),
    .X(_0008_));
 sky130_fd_sc_hd__dlymetal6s2s_1 _0705_ (.A(rst_n),
    .X(_0109_));
 sky130_fd_sc_hd__clkbuf_2 _0706_ (.A(ui_in[0]),
    .X(_0110_));
 sky130_fd_sc_hd__a21oi_1 _0707_ (.A1(\reg_a[1] ),
    .A2(_0110_),
    .B1(\accumulator[1] ),
    .Y(_0111_));
 sky130_fd_sc_hd__and3_1 _0708_ (.A(\accumulator[1] ),
    .B(\reg_a[1] ),
    .C(_0055_),
    .X(_0112_));
 sky130_fd_sc_hd__clkbuf_2 _0709_ (.A(net2),
    .X(_0113_));
 sky130_fd_sc_hd__or4bb_1 _0710_ (.A(_0111_),
    .B(_0112_),
    .C_N(_0113_),
    .D_N(\reg_a[0] ),
    .X(_0114_));
 sky130_fd_sc_hd__a2bb2o_1 _0711_ (.A1_N(_0111_),
    .A2_N(_0112_),
    .B1(_0068_),
    .B2(_0062_),
    .X(_0115_));
 sky130_fd_sc_hd__and3_1 _0712_ (.A(_0105_),
    .B(_0114_),
    .C(_0115_),
    .X(_0116_));
 sky130_fd_sc_hd__a21oi_1 _0713_ (.A1(_0114_),
    .A2(_0115_),
    .B1(_0105_),
    .Y(_0117_));
 sky130_fd_sc_hd__nor2_1 _0714_ (.A(_0116_),
    .B(_0117_),
    .Y(_0118_));
 sky130_fd_sc_hd__a22o_1 _0715_ (.A1(\accumulator[1] ),
    .A2(_0107_),
    .B1(_0118_),
    .B2(_0103_),
    .X(_0119_));
 sky130_fd_sc_hd__and2_1 _0716_ (.A(_0109_),
    .B(_0119_),
    .X(_0120_));
 sky130_fd_sc_hd__clkbuf_1 _0717_ (.A(_0120_),
    .X(_0009_));
 sky130_fd_sc_hd__clkbuf_2 _0718_ (.A(\reg_a[2] ),
    .X(_0121_));
 sky130_fd_sc_hd__a21oi_1 _0719_ (.A1(_0121_),
    .A2(_0056_),
    .B1(_0604_),
    .Y(_0122_));
 sky130_fd_sc_hd__and3_1 _0720_ (.A(\accumulator[2] ),
    .B(_0074_),
    .C(_0110_),
    .X(_0123_));
 sky130_fd_sc_hd__clkbuf_2 _0721_ (.A(net2),
    .X(_0124_));
 sky130_fd_sc_hd__and4bb_1 _0722_ (.A_N(_0122_),
    .B_N(_0123_),
    .C(_0069_),
    .D(_0124_),
    .X(_0125_));
 sky130_fd_sc_hd__o2bb2a_1 _0723_ (.A1_N(_0069_),
    .A2_N(_0068_),
    .B1(_0122_),
    .B2(_0123_),
    .X(_0126_));
 sky130_fd_sc_hd__nor2_1 _0724_ (.A(_0125_),
    .B(_0126_),
    .Y(_0127_));
 sky130_fd_sc_hd__and2b_1 _0725_ (.A_N(_0112_),
    .B(_0114_),
    .X(_0128_));
 sky130_fd_sc_hd__xnor2_1 _0726_ (.A(_0127_),
    .B(_0128_),
    .Y(_0129_));
 sky130_fd_sc_hd__and3_1 _0727_ (.A(_0073_),
    .B(_0062_),
    .C(_0129_),
    .X(_0130_));
 sky130_fd_sc_hd__a21oi_1 _0728_ (.A1(_0073_),
    .A2(_0062_),
    .B1(_0129_),
    .Y(_0131_));
 sky130_fd_sc_hd__nor2_1 _0729_ (.A(_0130_),
    .B(_0131_),
    .Y(_0132_));
 sky130_fd_sc_hd__nand2_1 _0730_ (.A(_0116_),
    .B(_0132_),
    .Y(_0133_));
 sky130_fd_sc_hd__or2_1 _0731_ (.A(_0116_),
    .B(_0132_),
    .X(_0134_));
 sky130_fd_sc_hd__a32o_1 _0732_ (.A1(_0103_),
    .A2(_0133_),
    .A3(_0134_),
    .B1(_0108_),
    .B2(_0604_),
    .X(_0135_));
 sky130_fd_sc_hd__and2_1 _0733_ (.A(_0109_),
    .B(_0135_),
    .X(_0136_));
 sky130_fd_sc_hd__clkbuf_1 _0734_ (.A(_0136_),
    .X(_0010_));
 sky130_fd_sc_hd__and2b_1 _0735_ (.A_N(_0128_),
    .B(_0127_),
    .X(_0137_));
 sky130_fd_sc_hd__a22oi_1 _0736_ (.A1(_0073_),
    .A2(_0070_),
    .B1(_0061_),
    .B2(_0078_),
    .Y(_0138_));
 sky130_fd_sc_hd__and4_1 _0737_ (.A(_0078_),
    .B(_0073_),
    .C(_0070_),
    .D(_0060_),
    .X(_0139_));
 sky130_fd_sc_hd__nor2_1 _0738_ (.A(_0138_),
    .B(_0139_),
    .Y(_0140_));
 sky130_fd_sc_hd__a21oi_1 _0739_ (.A1(_0079_),
    .A2(_0056_),
    .B1(\accumulator[3] ),
    .Y(_0141_));
 sky130_fd_sc_hd__and3_1 _0740_ (.A(\accumulator[3] ),
    .B(_0079_),
    .C(_0055_),
    .X(_0142_));
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
    .A2(_0404_),
    .B1(_0405_),
    .Y(_0406_));
 sky130_fd_sc_hd__xnor2_2 _1012_ (.A(_0403_),
    .B(_0406_),
    .Y(_0407_));
 sky130_fd_sc_hd__xor2_2 _1013_ (.A(_0385_),
    .B(_0407_),
    .X(_0408_));
 sky130_fd_sc_hd__and2b_1 _1014_ (.A_N(_0372_),
    .B(_0370_),
    .X(_0409_));
 sky130_fd_sc_hd__a21oi_2 _1015_ (.A1(_0346_),
    .A2(_0373_),
    .B1(_0409_),
    .Y(_0410_));
 sky130_fd_sc_hd__xnor2_2 _1016_ (.A(_0408_),
    .B(_0410_),
    .Y(_0411_));
 sky130_fd_sc_hd__a21oi_1 _1017_ (.A1(_0375_),
    .A2(_0379_),
    .B1(_0411_),
    .Y(_0412_));
 sky130_fd_sc_hd__a31o_1 _1018_ (.A1(_0375_),
    .A2(_0379_),
    .A3(_0411_),
    .B1(_0218_),
    .X(_0413_));
 sky130_fd_sc_hd__a2bb2o_1 _1019_ (.A1_N(_0412_),
    .A2_N(_0413_),
    .B1(_0039_),
    .B2(_0257_),
    .X(_0414_));
 sky130_fd_sc_hd__and2_1 _1020_ (.A(_0260_),
    .B(_0414_),
    .X(_0415_));
 sky130_fd_sc_hd__clkbuf_1 _1021_ (.A(_0415_),
    .X(_0018_));
 sky130_fd_sc_hd__or2_1 _1022_ (.A(_0408_),
    .B(_0410_),
    .X(_0416_));
 sky130_fd_sc_hd__inv_2 _1023_ (.A(_0416_),
    .Y(_0417_));
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
