lightrail-dev/new/tinytapeout/gl/tt_um_lightrail_nce.v

module tt_um_lightrail_nce (VGND,
    VPWR,
    clk,
    ena,
    rst_n,
    ui_in,
    uio_in,
    uio_oe,
    uio_out,
    uo_out);
 input VGND;
 input VPWR;
 input clk;
 input ena;
 input rst_n;
 input [7:0] ui_in;
 input [7:0] uio_in;
 output [7:0] uio_oe;
 output [7:0] uio_out;
 output [7:0] uo_out;

 wire net20;
 wire net21;
 wire net22;
 wire net23;
 wire net24;
 wire net25;
 wire net26;
 wire net27;
 wire net28;
 wire net29;
 wire net30;
 wire net31;
 wire net32;
 wire net33;
 wire net34;
 wire net35;
 wire _0000_;
 wire _0001_;
 wire _0002_;
 wire _0003_;
 wire _0004_;
 wire _0005_;
 wire _0006_;
 wire _0007_;
 wire _0008_;
 wire _0009_;
 wire _0010_;
 wire _0011_;
 wire _0012_;
 wire _0013_;
 wire _0014_;
 wire _0015_;
 wire _0016_;
 wire _0017_;
 wire _0018_;
 wire _0019_;
 wire _0020_;
 wire _0021_;
 wire _0022_;
 wire _0023_;
 wire _0024_;
 wire _0025_;
 wire _0026_;
 wire _0027_;
 wire _0028_;
 wire _0029_;
 wire _0030_;
 wire _0031_;
 wire _0032_;
 wire _0033_;
 wire _0034_;
 wire _0035_;
 wire _0036_;
 wire _0037_;
 wire _0038_;
 wire _0039_;
 wire _0040_;
 wire _0041_;
 wire _0042_;
 wire _0043_;
 wire _0044_;
 wire _0045_;
 wire _0046_;
 wire _0047_;
 wire _0048_;
 wire _0049_;
 wire _0050_;
 wire _0051_;
 wire _0052_;
 wire _0053_;
 wire _0054_;
 wire _0055_;
 wire _0056_;
 wire _0057_;
 wire _0058_;
 wire _0059_;
 wire _0060_;
 wire _0061_;
 wire _0062_;
 wire _0063_;
 wire _0064_;
 wire _0065_;
 wire _0066_;
 wire _0067_;
 wire _0068_;
 wire _0069_;
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
    .VNB(VGND));
 sky130_ef_sc_hd__decap_12 FILLER_0_4_177 (.VPWR(VPWR),
    .VGND(VGND),
    .VPB(VPWR),
    .VNB(VGND));
 sky130_fd_sc_hd__decap_6 FILLER_0_4_189 (.VGND(VGND),
    .VNB(VGND),
    .VPB(VPWR),
    .VPWR(VPWR));
 sky130_fd_sc_hd__fill_1 FILLER_0_4_195 (.VGND(VGND),
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
